ccadic/sharpikeebo/documentation/584001633806198522.jpg

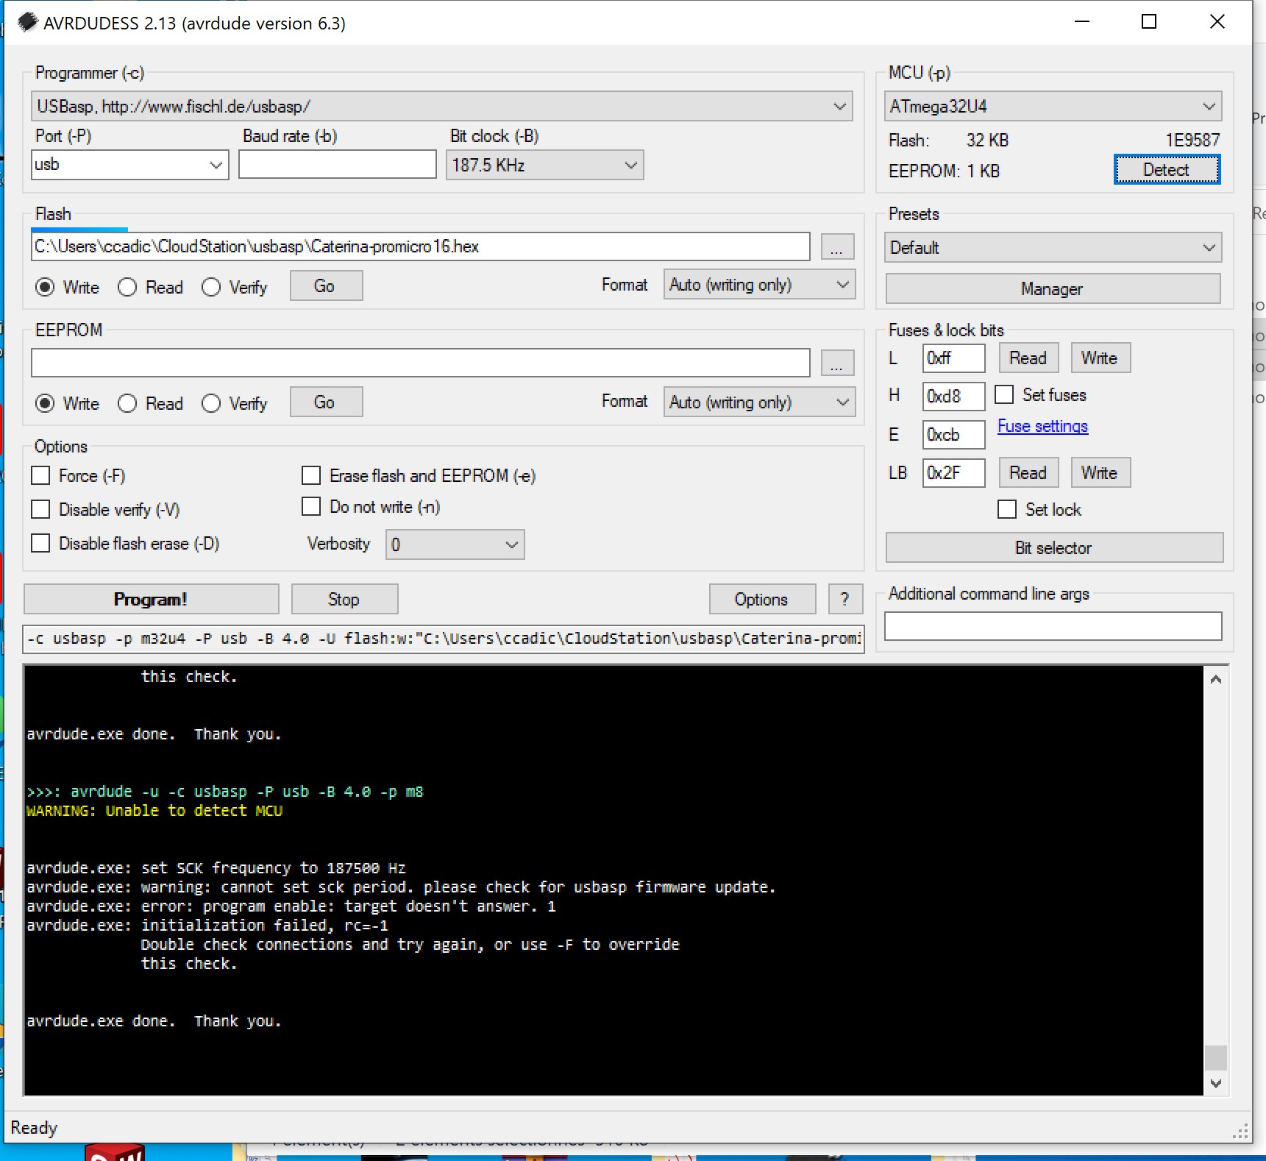
documentation/584001633806198522.jpg
