ccadic/sharpikeebo/update2026/enclosure2024/Untitled3.JPG

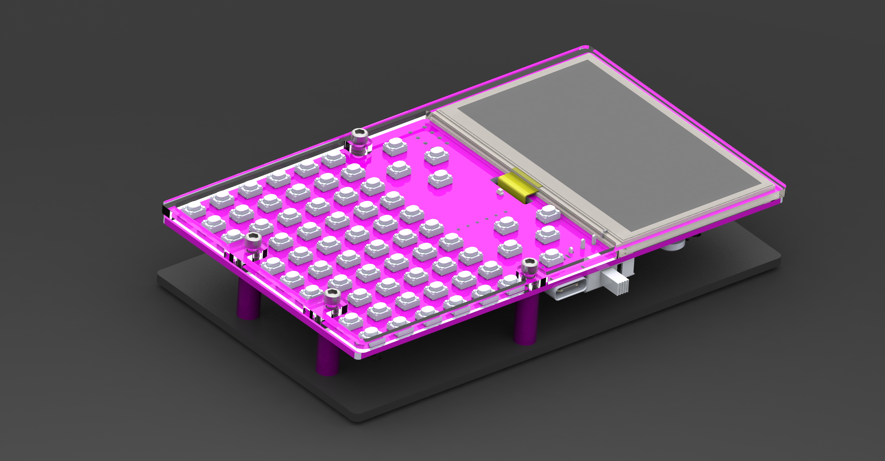
update2026/enclosure2024/Untitled3.JPG
